jpapiez/AntHead/STLs/Ducts/[a]_left_duct_HB92_x1.stl

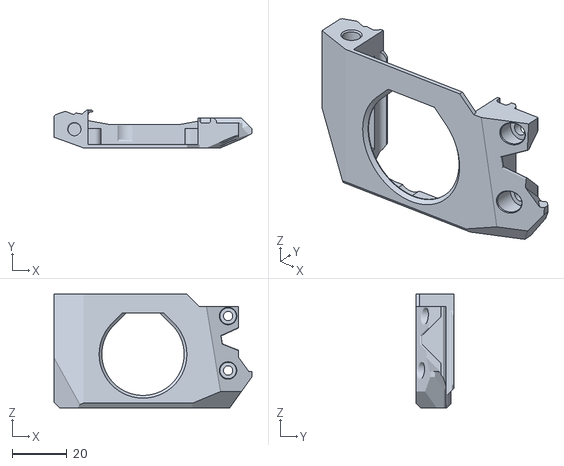
[picture p13: CAD file, 2024-12-22]
STLs/Ducts/[a]_left_duct_HB92_x1.stl
72.3 x 13.8 x 41.6
