jpapiez/AntHead/STLs/Extruders/G2/rear_plate.stl

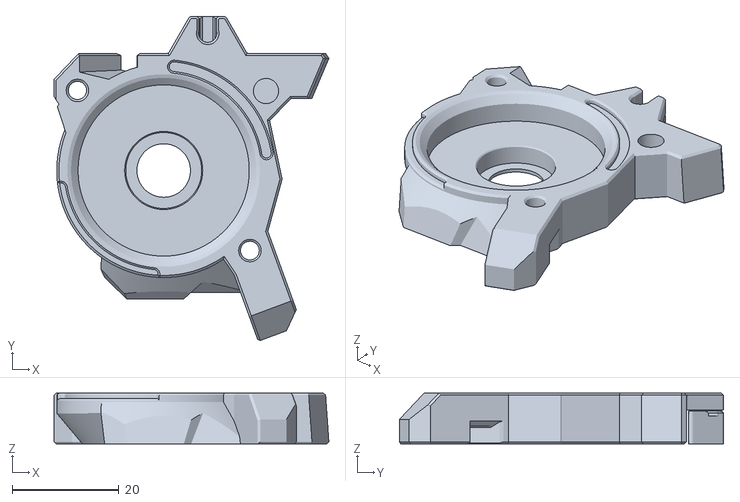
[picture p14: CAD file, 2024-12-22]
STLs/Extruders/G2/rear_plate.stl
51.4 x 60.6 x 9.53
