jpapiez/AntHead/STLs/Hotends/[a]_chube_for_ants_x1.stl

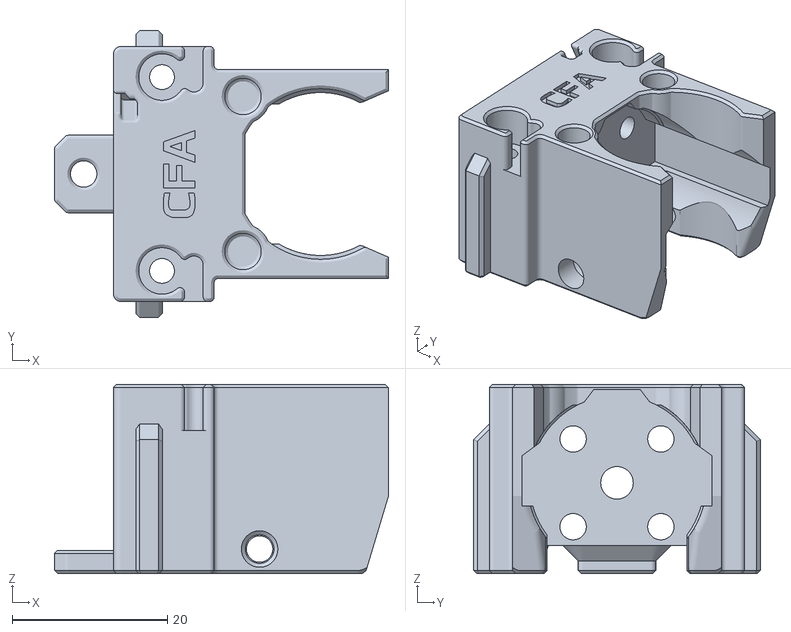
[picture p15: CAD file, 2026-02-26]
STLs/Hotends/[a]_chube_for_ants_x1.stl
43.1 x 37.0 x 24.4
