jpapiez/AntHead/UserMods/hartk/crossbow/STLs/[a]_depressor_arm_vitali_carriage.stl

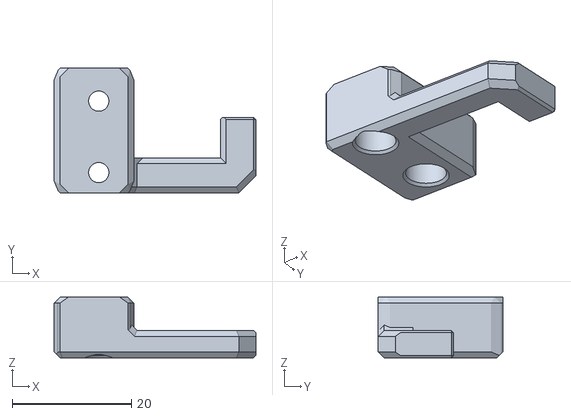
[picture p16: CAD file, 2026-01-15]
UserMods/hartk/crossbow/STLs/[a]_depressor_arm_vitali_carriage.stl
33.9 x 20.9 x 10.2
