jpapiez/AntHead/UserMods/hartk/crossbow/STLs/WWG2/wwg2_front_body_x1.stl

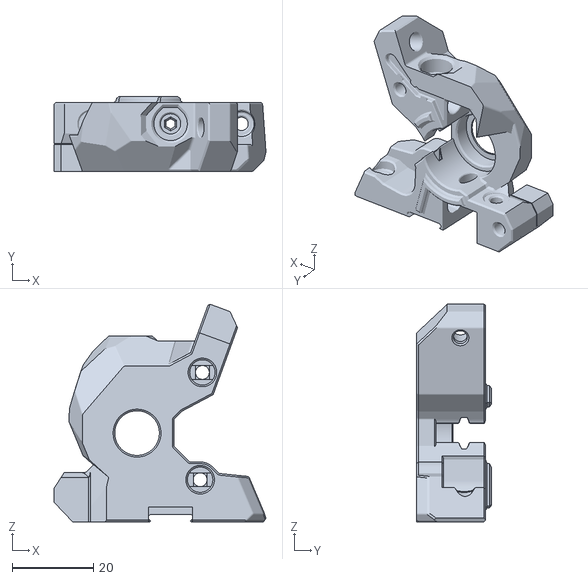
[picture p17: CAD file, 2026-01-15]
UserMods/hartk/crossbow/STLs/WWG2/wwg2_front_body_x1.stl
52.3 x 18.4 x 53.7
