jpapiez/AntHead/UserMods/hartk/leaf_cutter/STLs/Ducts/SF/[a]_left_duct_lc_x1.stl

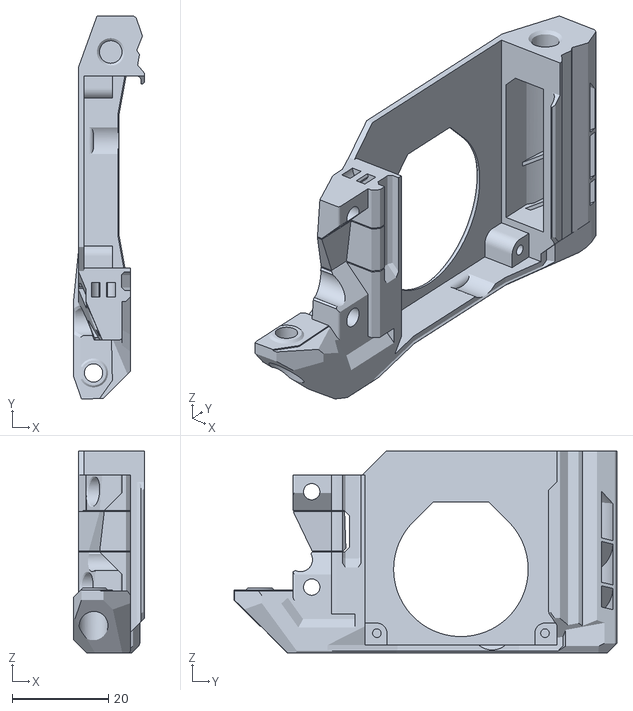
[picture p19: CAD file, 2026-02-26]
UserMods/hartk/leaf_cutter/STLs/Ducts/SF/[a]_left_duct_lc_x1.stl
14.8 x 79.7 x 42.0
