jpapiez/AntHead/UserMods/hartk/leaf_cutter/STLs/Ducts/UHF/[a]_left_duct_uhf_lc_x1.stl

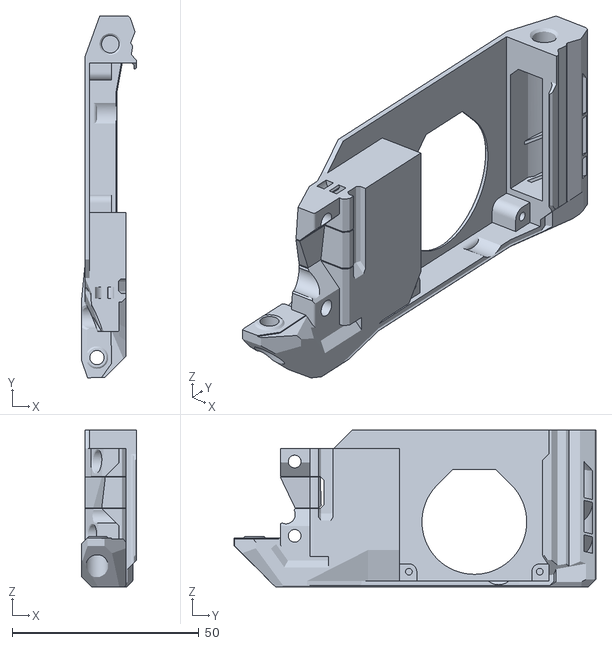
[picture p20: CAD file, 2026-02-26]
UserMods/hartk/leaf_cutter/STLs/Ducts/UHF/[a]_left_duct_uhf_lc_x1.stl
14.8 x 96.7 x 42.0
