jpapiez/AntHead/UserMods/hartk/leaf_cutter/STLs/Hotends/[a]_reVolcano_m2.5_x1.stl

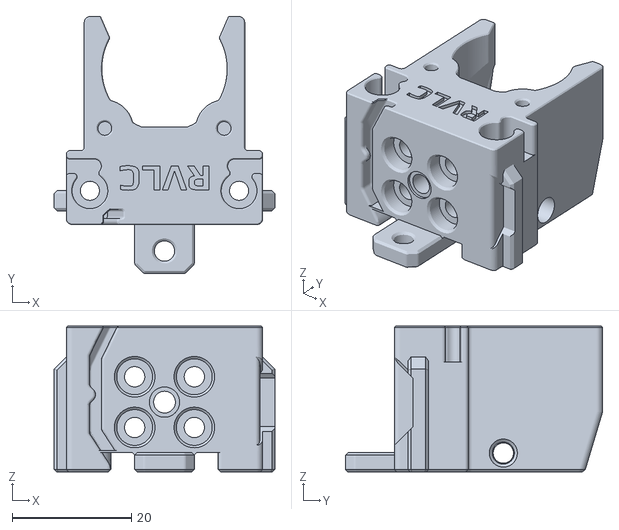
[picture p21: CAD file, 2026-02-26]
UserMods/hartk/leaf_cutter/STLs/Hotends/[a]_reVolcano_m2.5_x1.stl
37.0 x 43.1 x 24.4
