jpapiez/AntHead/UserMods/hartk/leaf_cutter/STLs/LeafCutter/cutting_arm_x1.stl

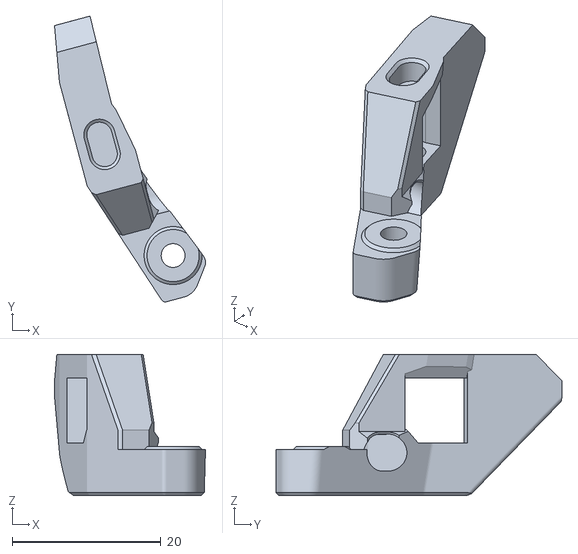
[picture p22: CAD file, 2026-02-26]
UserMods/hartk/leaf_cutter/STLs/LeafCutter/cutting_arm_x1.stl
20.3 x 38.5 x 19.0
