jpapiez/AntHead/UserMods/Main_Body_HexZero_logo/CAD/[o]_light_shield_HexZero_x1.stp

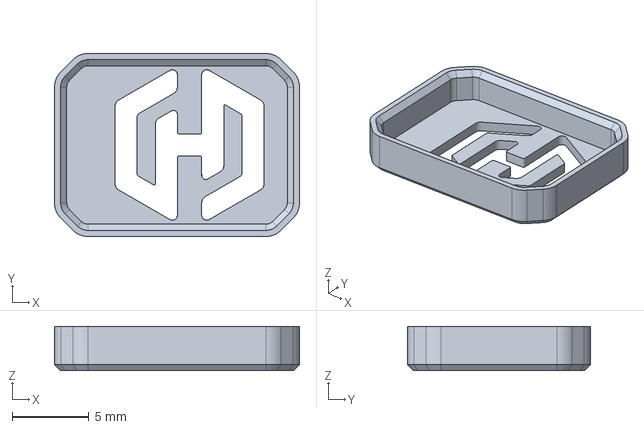
[picture p23: CAD file, 2024-12-22]
UserMods/Main_Body_HexZero_logo/CAD/[o]_light_shield_HexZero_x1.stp
16.0 x 11.9 x 2.90 mm
