jpapiez/AntHead/UserMods/WWG2_V0_Board_Mount/CAD/WWG2-V0-Board-Mount.step

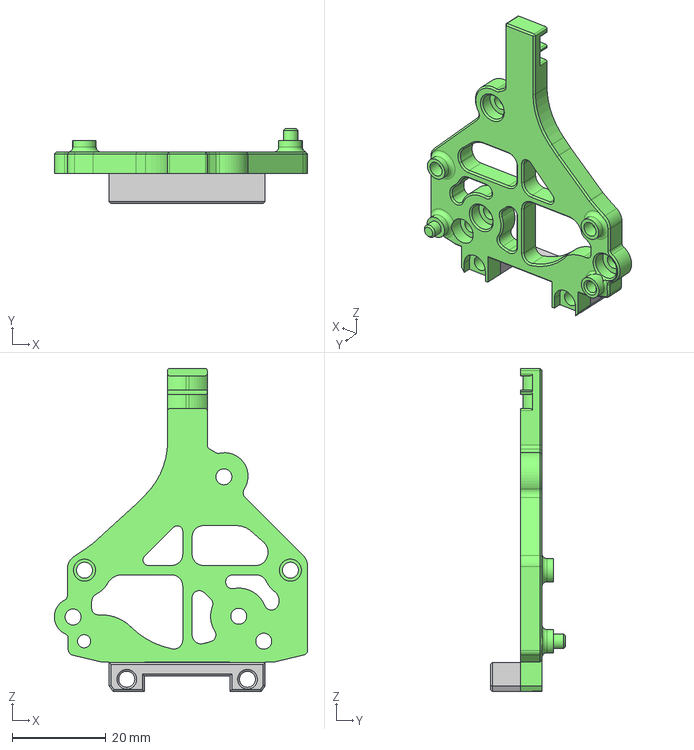
[picture p24: CAD file, 2025-12-20]
UserMods/WWG2_V0_Board_Mount/CAD/WWG2-V0-Board-Mount.step
53.9 x 16.0 x 68.8 mm
