jpapiez/AntHead/UserMods/WWG2_V0_Board_Mount/STL/board-mount.stl

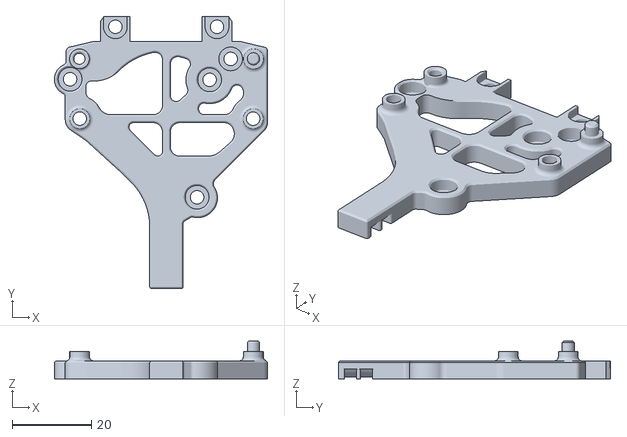
[picture p25: CAD file, 2025-12-20]
UserMods/WWG2_V0_Board_Mount/STL/board-mount.stl
53.9 x 68.8 x 9.60
