jpapiez/AntHead/UserMods/ZeroClick_left_ducting/CAD/[a]_HX0_left_duct_standard_x1.stp

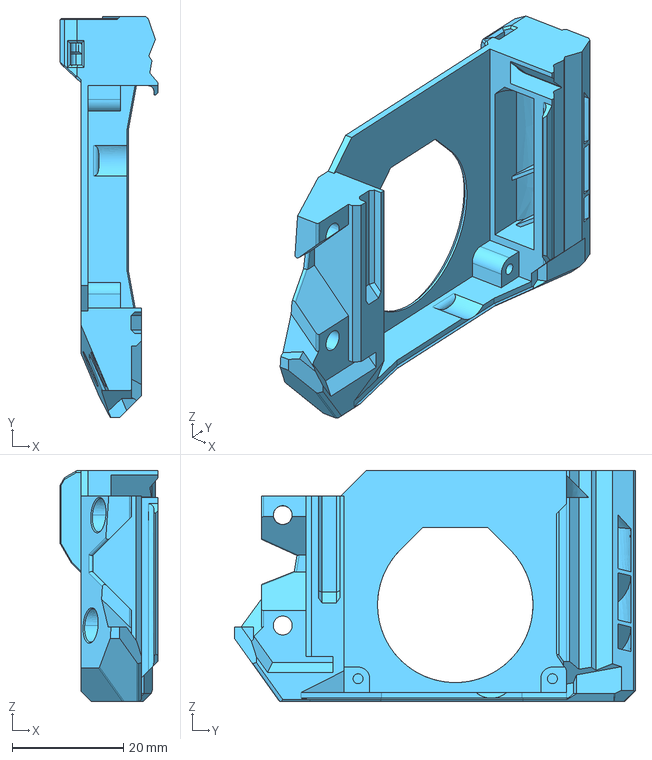
[picture p26: CAD file, 2024-12-22]
UserMods/ZeroClick_left_ducting/CAD/[a]_HX0_left_duct_standard_x1.stp
17.6 x 72.3 x 41.6 mm
