jpapiez/AntHead/STLs/Ducts/[a]_hf_left_duct_hb92_x1.stl

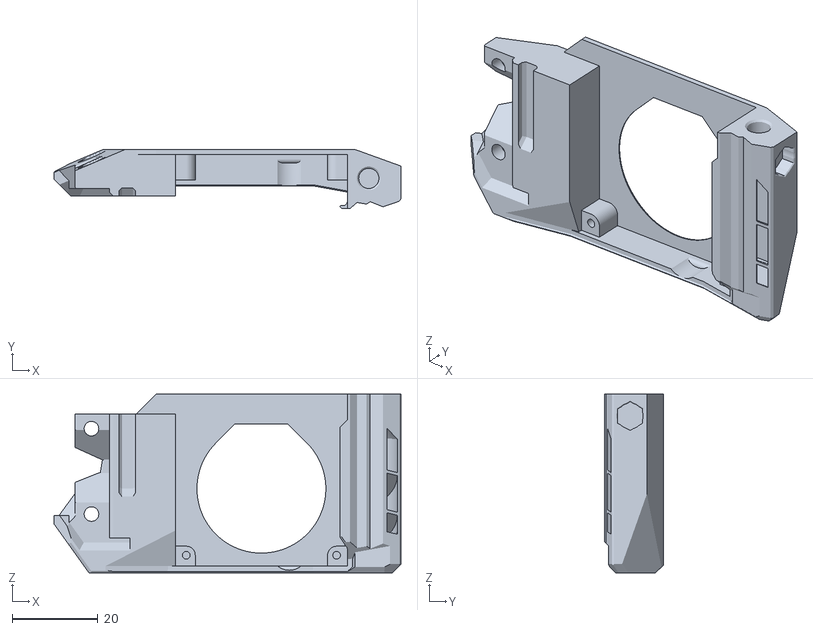
[picture p27: CAD file, 2024-12-22]
STLs/Ducts/[a]_hf_left_duct_hb92_x1.stl
80.8 x 13.8 x 41.6
