jpapiez/AntHead/UserMods/hartk/crossbow/STLs/anthead_crossbow_mount.stl

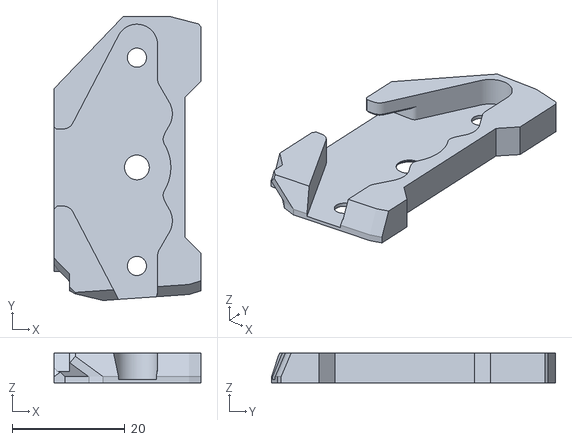
[picture p28: CAD file, 2026-01-15]
UserMods/hartk/crossbow/STLs/anthead_crossbow_mount.stl
26.1 x 50.4 x 5.30
