jpapiez/AntHead/UserMods/hartk/leaf_cutter/STLs/Ducts/HF/[a]_left_duct_hf_hb92_lc_x1.stl

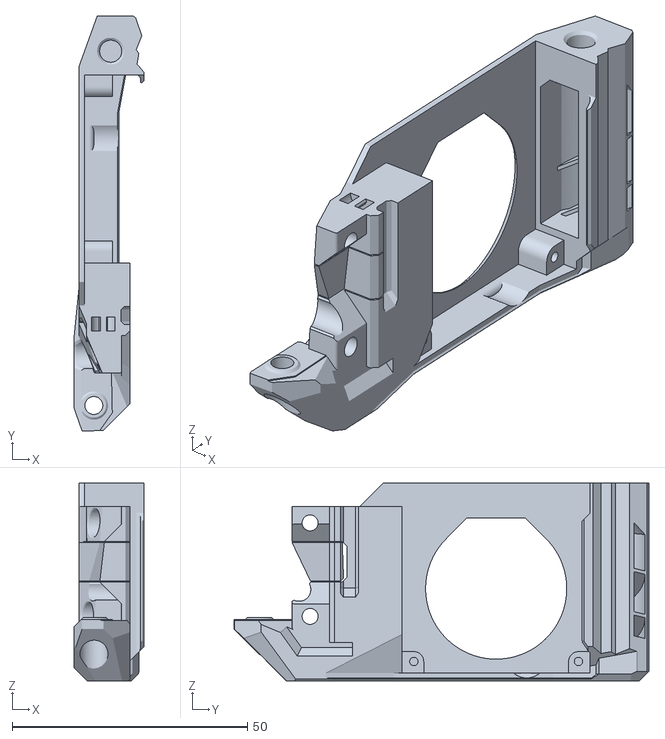
[picture p29: CAD file, 2026-02-26]
UserMods/hartk/leaf_cutter/STLs/Ducts/HF/[a]_left_duct_hf_hb92_lc_x1.stl
14.8 x 88.2 x 42.0
