jpapiez/AntHead/UserMods/hartk/leaf_cutter/STLs/LeafCutter/blade_check_tool.stl

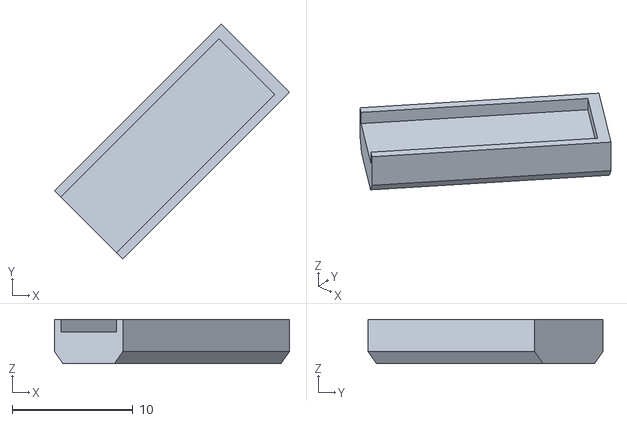
[picture p32: CAD file, 2026-02-26]
UserMods/hartk/leaf_cutter/STLs/LeafCutter/blade_check_tool.stl
19.5 x 19.5 x 3.68
