jpapiez/AntHead/UserMods/WWG2_V0_Board_Mount/STL/20-Spacer.stl

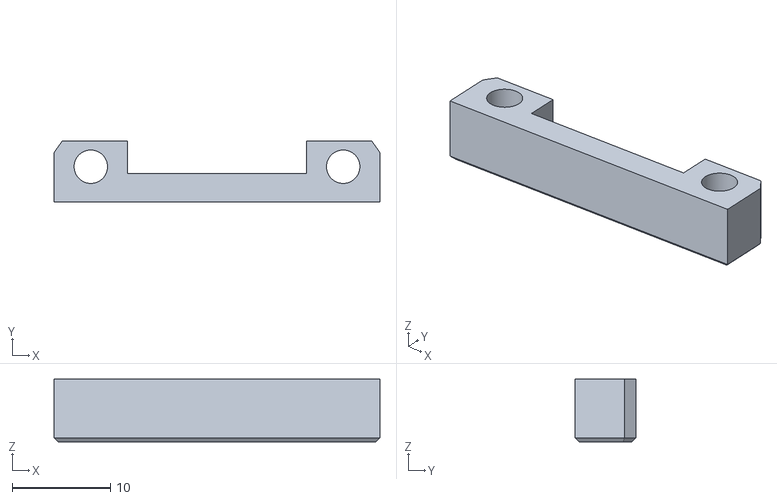
[picture p33: CAD file, 2025-12-20]
UserMods/WWG2_V0_Board_Mount/STL/20-Spacer.stl
33.2 x 6.17 x 6.40
