jpapiez/AntHead/UserMods/ZeroClick_left_ducting/CAD/[a]_HX0_right_duct_standard_x1.stp

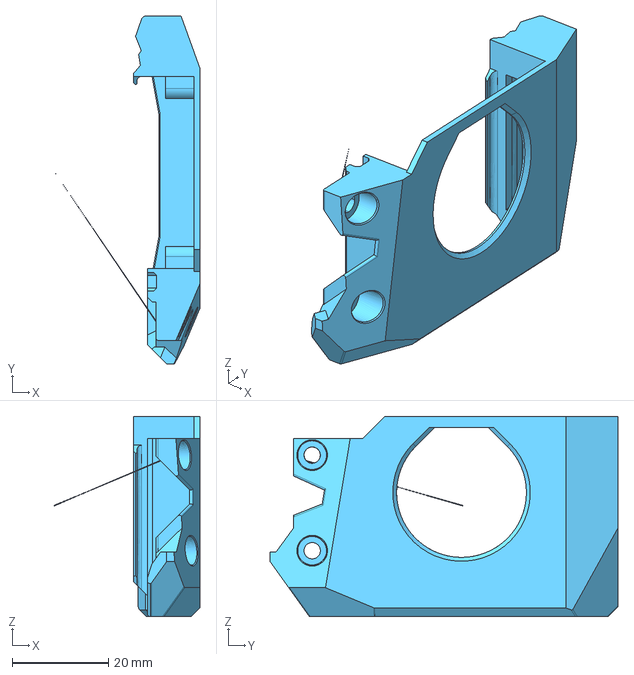
[picture p34: CAD file, 2024-12-22]
UserMods/ZeroClick_left_ducting/CAD/[a]_HX0_right_duct_standard_x1.stp
30.3 x 72.3 x 41.6 mm
