jpapiez/AntHead/STLs/Hotends/[a]_rapido_x1.stl

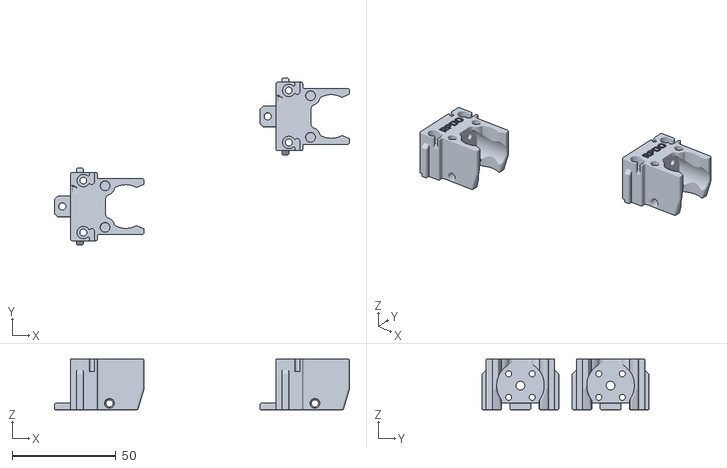
[picture p35: CAD file, 2026-02-26]
STLs/Hotends/[a]_rapido_x1.stl
141.9 x 80.3 x 24.4
