jpapiez/AntHead/UserMods/hartk/crossbow/STLs/[a]_depressor_arm_stock.stl

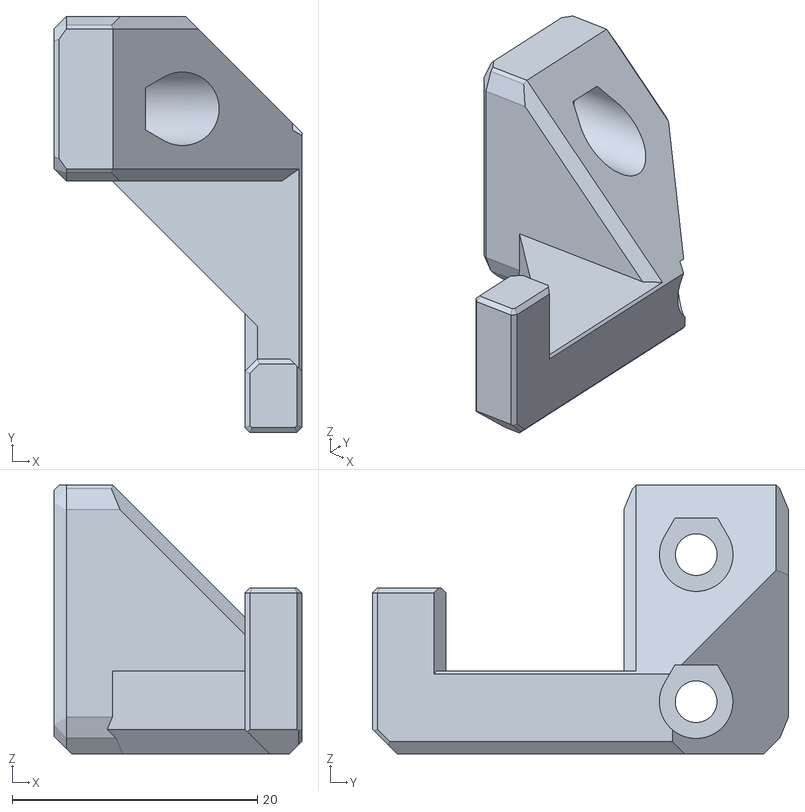
[picture p36: CAD file, 2026-01-15]
UserMods/hartk/crossbow/STLs/[a]_depressor_arm_stock.stl
20.2 x 33.9 x 21.9
