jpapiez/AntHead/UserMods/hartk/leaf_cutter/STLs/LeafCutter/[a]_26mm_blade_holder_x1.stl

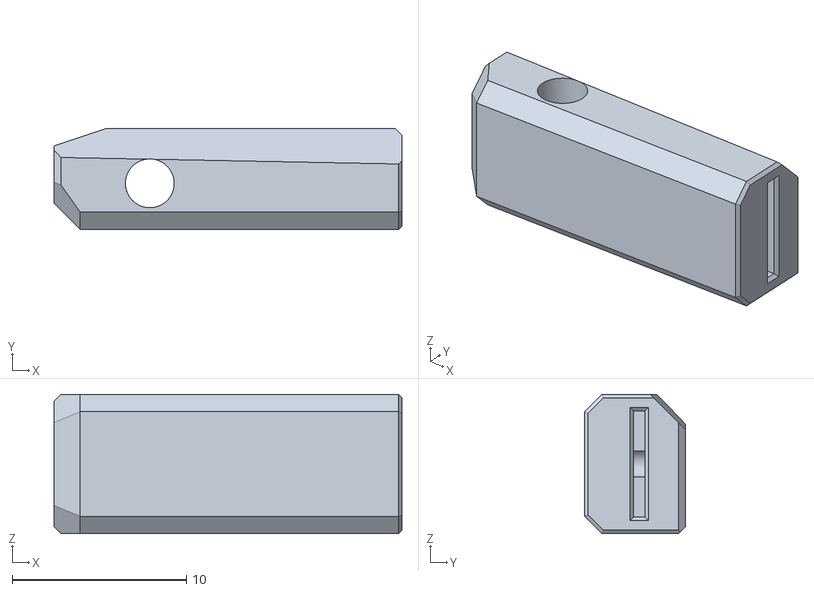
[picture p38: CAD file, 2026-02-26]
UserMods/hartk/leaf_cutter/STLs/LeafCutter/[a]_26mm_blade_holder_x1.stl
20.0 x 5.80 x 8.00
