jpapiez/AntHead/UserMods/Main_Body_HexZero_logo/CAD/[c]_diffuser_HexZero_x1.stp

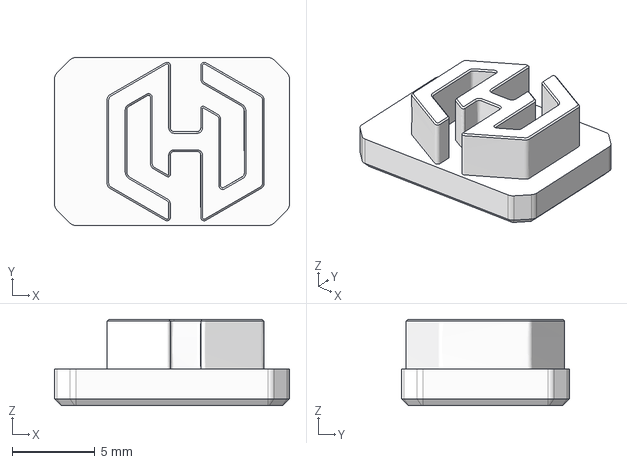
[picture p39: CAD file, 2024-12-22]
UserMods/Main_Body_HexZero_logo/CAD/[c]_diffuser_HexZero_x1.stp
14.2 x 10.1 x 5.20 mm
