jpapiez/AntHead/UserMods/WWG2_V0_Board_Mount/STL/16-Spacer.stl

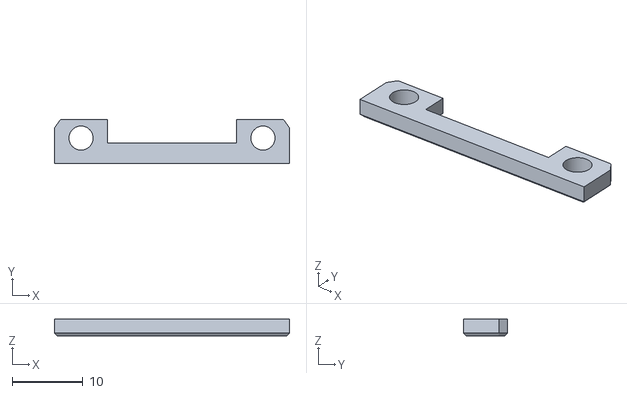
[picture p40: CAD file, 2025-12-20]
UserMods/WWG2_V0_Board_Mount/STL/16-Spacer.stl
33.2 x 6.17 x 2.40
