jpapiez/AntHead/STLs/Ducts/[a]_right_duct_standard_x1.stl

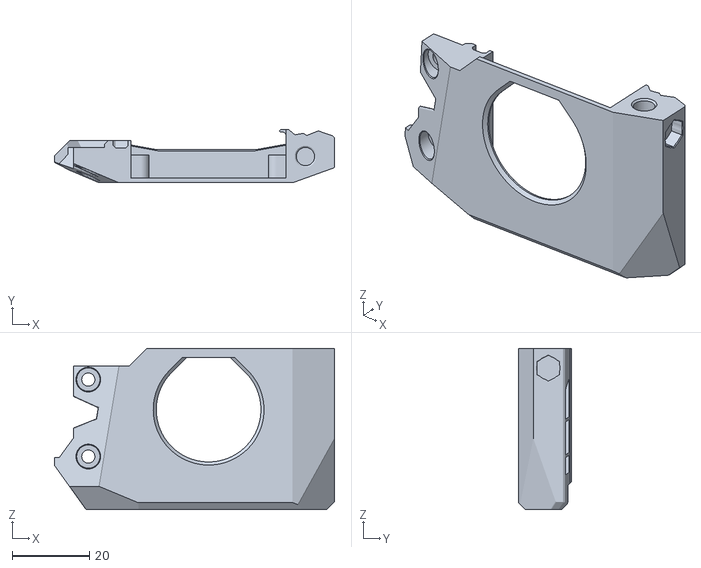
[picture p43: CAD file, 2024-12-22]
STLs/Ducts/[a]_right_duct_standard_x1.stl
72.3 x 13.8 x 41.6
