jpapiez/AntHead/STLs/Ducts/[a]_hf_right_duct_x1.stl

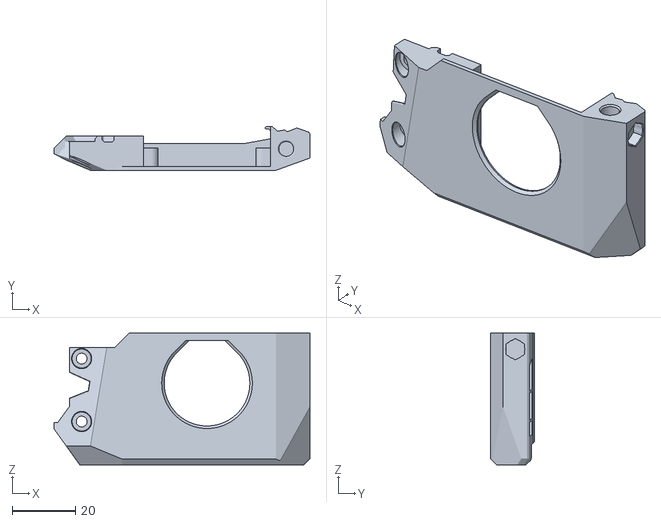
[picture p45: CAD file, 2024-12-22]
STLs/Ducts/[a]_hf_right_duct_x1.stl
80.8 x 13.8 x 41.6
