jpapiez/AntHead/STLs/Hotends/[a]_dragon_x1.stl

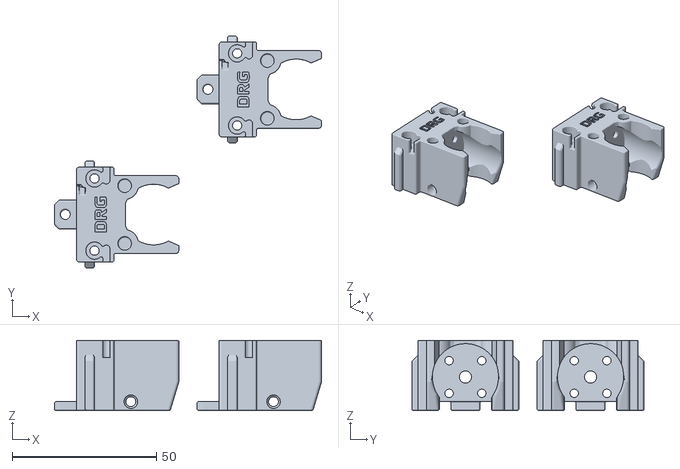
[picture p47: CAD file, 2026-02-26]
STLs/Hotends/[a]_dragon_x1.stl
92.5 x 80.3 x 24.4
