jpapiez/AntHead/STLs/Ducts/[a]_uhf_left_duct_hb92_x1.stl

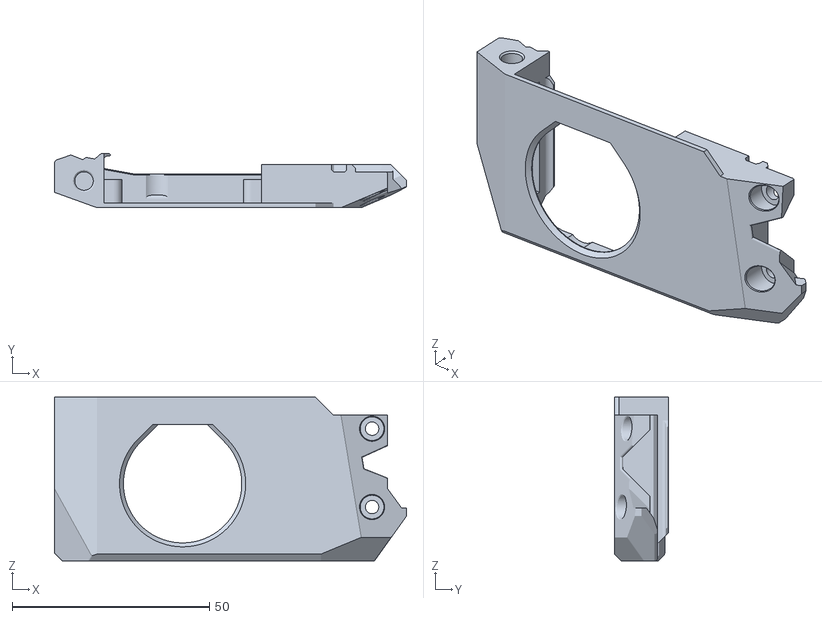
[picture p48: CAD file, 2024-12-22]
STLs/Ducts/[a]_uhf_left_duct_hb92_x1.stl
89.3 x 13.8 x 41.6
