jpapiez/AntHead/STLs/Hotends/[a]_bambu_x1.stl

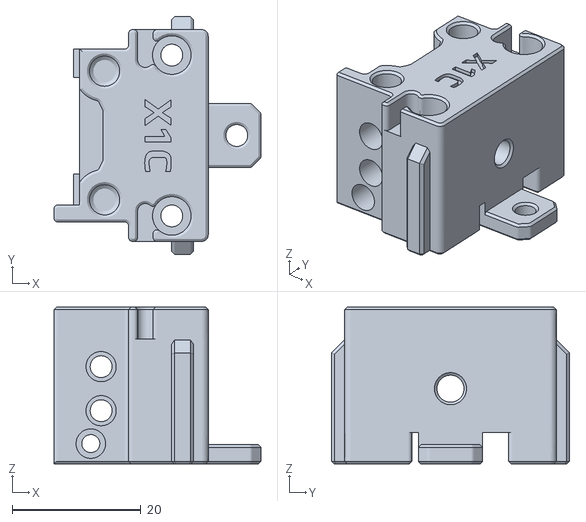
[picture p50: CAD file, 2024-12-03]
STLs/Hotends/[a]_bambu_x1.stl
32.2 x 37.0 x 24.4
